uwulises/ME5120_quadruped/control/leg_control/peripheral_motor/peripheral_motor.ino

#include "spi_msg.h"
#include "drv.h"
uint8_t target_angle = 0;
uint8_t current_position = 0;

void setup() {
  drv_setup();
  spi_slave_init();
}

void loop() {
  // main FOC algorithm function
  motor_loop();
  if (spi_is_readable(spi_default)){
  target_angle=spi_slave_exchange(current_position);
  update_target(target_angle);}
  if (target_angle!=current_position){Serial.println(target_angle);}
  current_position = target_angle;
}
