uwulises/ME5120_quadruped/control/leg_control/leg_position_control/spi_msg.h

#ifndef SPI_MSG_H
#define SPI_MSG_H
#include <stdint.h>
#include <stdio.h>
#include <cstring>
#include "pico/stdlib.h"
#include "hardware/spi.h"
#include "pico/binary_info.h"

#define BUF_LEN 1

// Define CS pins for each slave
#define CS_SLAVE1 20
#define CS_SLAVE2 21

void spi_master_init();
uint8_t spi_slave_exchange(uint8_t current_position);
void spi_slave_init();

uint8_t spi_exchange_angle(uint cs_pin, uint8_t target_angle);

void select_slave(uint cs_pin);
void deselect_slave(uint cs_pin);

#endif
